TUDSSL/DIPS/int-debugger-firmware/src/gdb_main.c

/*
* This file is part of the Black Magic Debug project.
*
* Copyright (C) 2011  Black Sphere Technologies Ltd.
* Written by Gareth McMullin <gareth@blacksphere.co.nz>
*
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
* You should have received a copy of the GNU General Public License
* along with this program.  If not, see <http://www.gnu.org/licenses/>.
*/

/* This file implements the GDB Remote Serial Debugging protocol as
* described in "Debugging with GDB" build from GDB source.
*
* Originally written for GDB 6.8, updated and tested with GDB 7.2.
*/

#include "general.h"
#include "ctype.h"
#include "hex_utils.h"
#include "gdb_if.h"
#include "gdb_packet.h"
#include "gdb_main.h"
#include "gdb_hostio.h"
#include "target.h"
#include "command.h"
#include "crc32.h"
#include "morse.h"
#include "exception.h"
#include "spi.h"
#include <alloca.h>

enum gdb_signal {
   GDB_SIGINT = 2,
   GDB_SIGTRAP = 5,
   GDB_SIGSEGV = 11,
   GDB_SIGLOST = 29,
};

#define BUF_SIZE	1024U

#define ERROR_IF_NO_TARGET()	\
	if(!cur_target) { target_lost(); break; }

typedef struct
{
   const char *cmd_prefix;
   void (*func)(const char *packet, size_t len);
} cmd_executer;

static char pbuf[BUF_SIZE + 1U];

static target *cur_target;
static target *last_target;
static bool gdb_needs_detach_notify = false;

static void handle_q_packet(char *packet, size_t len);
static void handle_v_packet(char *packet, size_t len);
static void handle_z_packet(char *packet, size_t len);
static void handle_kill_target(void);

unsigned int times_intermittent = 0;
bool m_interrupt_on_power_failure = false;
arch_mode_t m_current_architecture = UNKNOWN_ARCH;
operation_mode_t m_debugger_mode = MODE_REGULAR;
bool disable_supply_after_next_continue = false;

static void gdb_target_destroy_callback(struct target_controller *tc, target *t)
{
   (void)tc;
   if (cur_target == t) {
       cur_target = NULL;
       gdb_needs_detach_notify = true;
   }

   if (last_target == t)
       last_target = NULL;
}

static void gdb_target_printf(struct target_controller *tc,
                             const char *fmt, va_list ap)
{
   (void)tc;
   gdb_voutf(fmt, ap);
}

static struct target_controller gdb_controller = {
   .destroy_callback = gdb_target_destroy_callback,
   .printf = gdb_target_printf,

   .open = hostio_open,
   .close = hostio_close,
   .read = hostio_read,
   .write = hostio_write,
   .lseek = hostio_lseek,
   .rename = hostio_rename,
   .unlink = hostio_unlink,
   .stat = hostio_stat,
   .fstat = hostio_fstat,
   .gettimeofday = hostio_gettimeofday,
   .isatty = hostio_isatty,
   .system = hostio_system,
};

void halt_gdb_main_loop(){
    target_addr_t watch;
    enum target_halt_reason reason;

    if (!cur_target) {
        /* Report "target exited" if no target */
        gdb_putpacketz("W00");
        return;
    }

    /* Wait for target halt */
    platform_timeout timeout;
Again:
    if(m_debugger_mode != MODE_PROFILE) disable_supply();
    while(!(reason = target_halt_poll(cur_target, &watch))) {
        if(false){
            char c = (char)gdb_if_getchar_to(0);
            if(c == '\x03' || c == '\x04')
            target_halt_request(cur_target);
        }
    }
    SET_RUN_STATE(0);

    /* Translate reason to GDB signal */
    switch (reason) {
        case TARGET_HALT_BREAKPOINT:
            if(m_debugger_mode != MODE_PROFILE) enable_supply();
            if(m_current_architecture != MSP_ARCH){
                // Not sure why this is implemented but it is unnessecary for the MSP arch
                platform_timeout_set(&timeout, 200);
                while ((reason = target_halt_poll(cur_target, &watch)) == TARGET_HALT_BREAKPOINT){
                    if (platform_timeout_is_expired(&timeout))
                        break;
                }
            }
            if (reason == TARGET_HALT_BREAKPOINT){
                gdb_putpacket_f("T%02X", GDB_SIGTRAP);
                break;
            } else if (reason != TARGET_HALT_INTERMITTENT){
                goto Again;
            }
            /* Fallthrough for TARGET_HALT_INTERMITTENT */
        case TARGET_HALT_INTERMITTENT:
            if(m_debugger_mode != MODE_PROFILE) disable_supply();
            if (intermittent_mode){
                morse("I.", false);
                target_lost();
            }
            else{
                gdb_putpacket_f("X%02X", GDB_SIGLOST);
                target_list_free_extended();
                morse("TARGET LOST.", true);
            }
            break;
        case TARGET_HALT_REQUEST:
            if(m_debugger_mode != MODE_PROFILE) enable_supply();
            gdb_putpacket_f("T%02X", GDB_SIGINT);
            break;
        case TARGET_HALT_WATCHPOINT:
            if(m_debugger_mode != MODE_PROFILE) enable_supply();
            gdb_putpacket_f("T%02Xwatch:%08X;", GDB_SIGTRAP, watch);
            break;
        case TARGET_HALT_FAULT:
            gdb_putpacket_f("T%02X", GDB_SIGSEGV);
            break;
        default:
            if(m_debugger_mode != MODE_PROFILE) enable_supply();
            gdb_putpacket_f("T%02X", GDB_SIGTRAP);
    }
}

int gdb_main_loop(struct target_controller *tc, bool in_syscall)
{
   bool single_step = false;

   /* GDB protocol main loop */
   while (1) {
       // When device was intermittent:
       if (!target_available()){
           // Reconnect procedure:
           // Check if device is reachable again or return
           // Reconnect:
           // Send SWD->JTAG command
           // Compare IDCODE with old IDCODE when different -> exception
           // Turn on Debug Port
           // Get AP en DP information from cache
           // Write AP select and unlock the AP's
           // Halt and Enable Supply
           // Reconfigure breakpoints
           // Continue execution + Disable Supply

           // Take note of the frees and memory allocations
           // Maybe when device is deattached, free more rather then when connection is lost
           target_list_free();

           SET_IDLE_STATE(false);
           SET_ERROR_STATE(true);
           int devs = -1;
           bool do_halt = false;
           volatile struct exception e;
           // Find the target or catch

           while(devs <= 0){
                char c = (char)gdb_if_getchar_to(0);
                if(c == '\x03' || c == '\x04'){
                    enable_supply();
                    do_halt = true;
                }
               
               TRY_CATCH (e, EXCEPTION_ALL) {
                switch (m_current_architecture)
                {
                    case MSP_ARCH:
                        devs = sbw_scan(0);                    
                        break;
                    case ARM_ARCH:
                        devs = adiv5_swdp_scan(0);
                        break;
                    default:
                        devs = adiv5_swdp_scan(0);
                        if(devs <= 0){
                                devs = sbw_scan(0);
                        }
                        break;
                }
               }
           }
           
           enable_supply();
           if(m_debugger_mode == MODE_PROFILE){
              disable_supply_after_next_continue = true;
           }

           SET_ERROR_STATE(false);
           times_intermittent++;

           // try reconnecting
           cur_target = target_attach_n(1, &gdb_controller);

           // retransmit breakpoints/watchpoints
           target_restore_breakpoints(cur_target);
           if (!do_halt && !m_interrupt_on_power_failure){
               target_halt_resume(cur_target, single_step);
               SET_RUN_STATE(true);
               halt_gdb_main_loop();
               break;
           }
           gdb_putpacket_f("T%02X", GDB_SIGINT);
       }

       SET_IDLE_STATE(1);
       size_t size = gdb_getpacket(pbuf, BUF_SIZE);
       // If port closed and target detached, stay idle
       if ((pbuf[0] != 0x04) || cur_target) {
           SET_IDLE_STATE(0);
       }
       switch(pbuf[0]) {
           /* Implementation of these is mandatory! */
           case 'g': { /* 'g': Read general registers */
               ERROR_IF_NO_TARGET();
               uint8_t gp_regs[target_regs_size(cur_target)];
               target_regs_read(cur_target, gp_regs);
               gdb_putpacket(hexify(pbuf, gp_regs, sizeof(gp_regs)), sizeof(gp_regs) * 2U);
               break;
           }
           case 'm': {	/* 'm addr,len': Read len bytes from addr */
               uint32_t addr, len;
               ERROR_IF_NO_TARGET();
               sscanf(pbuf, "m%" SCNx32 ",%" SCNx32, &addr, &len);
               if (len > sizeof(pbuf) / 2) {
                   gdb_putpacketz("E02");
                   break;
               }
               DEBUG_GDB("m packet: addr = %" PRIx32 ", len = %" PRIx32 "\n",
                         addr, len);
               uint8_t mem[len];
               if (target_mem_read(cur_target, mem, addr, len))
                   gdb_putpacketz("E01");
               else
                   gdb_putpacket(hexify(pbuf, mem, len), len * 2U);
               break;
           }
           case 'G': {	/* 'G XX': Write general registers */
               ERROR_IF_NO_TARGET();
               uint8_t gp_regs[target_regs_size(cur_target)];
               unhexify(gp_regs, &pbuf[1], sizeof(gp_regs));
               target_regs_write(cur_target, gp_regs);
               gdb_putpacketz("OK");
               break;
           }
           case 'M': { /* 'M addr,len:XX': Write len bytes to addr */
               uint32_t addr = 0;
               uint32_t len = 0;
               int hex;
               ERROR_IF_NO_TARGET();
               sscanf(pbuf, "M%" SCNx32 ",%" SCNx32 ":%n", &addr, &len, &hex);
               if (len > (unsigned)(size - hex) / 2) {
                   gdb_putpacketz("E02");
                   break;
               }
               DEBUG_GDB("M packet: addr = %" PRIx32 ", len = %" PRIx32 "\n",
                         addr, len);
               uint8_t mem[len];
               unhexify(mem, pbuf + hex, len);
               if (target_mem_write(cur_target, addr, mem, len))
                   gdb_putpacketz("E01");
               else
                   gdb_putpacketz("OK");
               break;
           }
           /* '[m|M|g|G|c][thread-id]' : Set the thread ID for the given subsequent operation
        * (we don't actually care which as we only care about the TID for whether to send OK or an error)
            */
           case 'H': {
               char operation = 0;
               uint32_t thread_id = 0;
               sscanf(pbuf, "H%c%" SCNx32, &operation, &thread_id);
               if (thread_id <= 1)
                   gdb_putpacketz("OK");
               else
                   gdb_putpacketz("E01");
               break;
           }
           case 's':	/* 's [addr]': Single step [start at addr] */
               single_step = true;
               /* fall through */
           case 'c':	/* 'c [addr]': Continue [at addr] */
               if (!cur_target) {
                   gdb_putpacketz("X1D");
                   break;
               }

               target_halt_resume(cur_target, single_step);
               SET_RUN_STATE(1);
               single_step = false;
               /* fall through */
           case '?': {	/* '?': Request reason for target halt */
               /* This packet isn't documented as being mandatory,
            * but GDB doesn't work without it. */
               halt_gdb_main_loop();
              break;
           }

           /* Optional GDB packet support */
           case 'p': { /* Read single register */
               ERROR_IF_NO_TARGET();
               uint32_t reg;
               sscanf(pbuf, "p%" SCNx32, &reg);
               uint8_t val[8];
               size_t s = target_reg_read(cur_target, reg, val, sizeof(val));
               if (s > 0)
                   gdb_putpacket(hexify(pbuf, val, s), s * 2);
               else
                   target_lost();
               break;
           }
           case 'P': { /* Write single register */
               ERROR_IF_NO_TARGET();
               uint32_t reg;
               int n;
               sscanf(pbuf, "P%" SCNx32 "=%n", &reg, &n);
               // TODO: FIXME, VLAs considered harmful.
               uint8_t val[strlen(&pbuf[n]) / 2];
               unhexify(val, pbuf + n, sizeof(val));
               if (target_reg_write(cur_target, reg, val, sizeof(val)) > 0)
                   gdb_putpacketz("OK");
               else
                   target_lost();
               break;
           }

           case 'F':	/* Semihosting call finished */
               if (in_syscall)
                   return hostio_reply(tc, pbuf, size);
               else {
                   DEBUG_GDB("*** F packet when not in syscall! '%s'\n", pbuf);
                   gdb_putpacketz("");
               }
               break;

           case '!':	/* Enable Extended GDB Protocol. */
               /* This doesn't do anything, we support the extended
            * protocol anyway, but GDB will never send us a 'R'
            * packet unless we answer 'OK' here.
                */
               gdb_putpacketz("OK");
               break;

           case 0x04:
           case 'D':	/* GDB 'detach' command. */
               if(cur_target) {
                   SET_RUN_STATE(1);
                   target_detach(cur_target);
                   last_target = cur_target;
                   target_list_free_extended();
                   cur_target = NULL;
               }
               if (pbuf[0] == 'D')
                   gdb_putpacketz("OK");

               if(m_debugger_mode != MODE_PROFILE) disable_supply();
               break;

           case 'k':	/* Kill the target */
               handle_kill_target();
               break;

           case 'r':	/* Reset the target system */
           case 'R':	/* Restart the target program */
               if (cur_target)
                   target_reset(cur_target);
               else if (last_target) {
                   cur_target = target_attach(last_target, &gdb_controller);
                   if (cur_target)
                       morse(NULL, false);
                   target_reset(cur_target);
               }
               break;

           case 'X': { /* 'X addr,len:XX': Write binary data to addr */
               uint32_t addr, len;
               int bin;
               ERROR_IF_NO_TARGET();
               sscanf(pbuf, "X%" SCNx32 ",%" SCNx32 ":%n", &addr, &len, &bin);
               if (len > (unsigned)(size - bin)) {
                   gdb_putpacketz("E02");
                   break;
               }
               DEBUG_GDB("X packet: addr = %" PRIx32 ", len = %" PRIx32 "\n",
                         addr, len);
               if (target_mem_write(cur_target, addr, pbuf + bin, len))
                   gdb_putpacketz("E01");
               else
                   gdb_putpacketz("OK");
               break;
           }

           case 'q':	/* General query packet */
               handle_q_packet(pbuf, size);
               break;

           case 'v':	/* Verbose command packet */
               handle_v_packet(pbuf, size);
               break;

           /* These packet implement hardware break-/watchpoints */
           case 'Z':	/* Z type,addr,len: Set breakpoint packet */
           case 'z':	/* z type,addr,len: Clear breakpoint packet */
               ERROR_IF_NO_TARGET();
               handle_z_packet(pbuf, size);
               break;

           default: 	/* Packet not implemented */
               DEBUG_GDB("*** Unsupported packet: %s\n", pbuf);
               gdb_putpacketz("");
       }
   }
}

static bool exec_command(char *packet, const size_t length, const cmd_executer *exec)
{
   while (exec->cmd_prefix) {
       const size_t prefix_length = strlen(exec->cmd_prefix);
       if (!strncmp(packet, exec->cmd_prefix, prefix_length)) {
           exec->func(packet + prefix_length, length - prefix_length);
           return true;
       }
       ++exec;
   }
   return false;
}

static void exec_q_rcmd(const char *packet, const size_t length)
{
   /* calculate size and allocate buffer for command */
   const size_t datalen = length / 2U;
   // This needs replacing with something more sensible.
   // It should be pinging -Wvla among other things, and it failing is straight-up UB
   char *data = alloca(datalen + 1);
   /* dehexify command */
   unhexify(data, packet, datalen);
   data[datalen] = 0;	/* add terminating null */

   const int c = command_process(cur_target, data);
   if (c < 0)
       gdb_putpacketz("");
   else if (c == 0)
       gdb_putpacketz("OK");
   else
       gdb_putpacket(hexify(pbuf, "Failed\n", strlen("Failed\n")),
                     2 * strlen("Failed\n"));
}

static void handle_q_string_reply(const char *reply, const char *param)
{
   const size_t reply_length = strlen(reply);
   uint32_t addr = 0;
   uint32_t len = 0;

   if (sscanf(param, "%08" PRIx32 ",%08" PRIx32, &addr, &len) != 2) {
       gdb_putpacketz("E01");
       return;
   }
   if (addr > reply_length) {
       gdb_putpacketz("E01");
       return;
   }
   if (addr == reply_length) {
       gdb_putpacketz("l");
       return;
   }
   size_t output_len = reply_length - addr;
   if (output_len > len)
       output_len = len;
   gdb_putpacket2("m", 1U, reply + addr, output_len);
}

static void exec_q_supported(const char *packet, const size_t length)
{
   (void)packet;
   (void)length;
   gdb_putpacket_f("PacketSize=%X;qXfer:memory-map:read+;qXfer:features:read+", BUF_SIZE);
}

static void exec_q_memory_map(const char *packet, const size_t length)
{
   (void)packet;
   (void)length;
   /* Read target XML memory map */
   if ((!cur_target) && last_target) {
       /* Attach to last target if detached. */
       cur_target = target_attach(last_target,
                                  &gdb_controller);
   }
   if (!cur_target) {
       gdb_putpacketz("E01");
       return;
   }
   char buf[1024];
   target_mem_map(cur_target, buf, sizeof(buf)); /* Fixme: Check size!*/
   handle_q_string_reply(buf, packet);
}

static void exec_q_feature_read(const char *packet, const size_t length)
{
   (void)length;
   /* Read target description */
   if ((!cur_target) && last_target) {
       /* Attach to last target if detached. */
       cur_target = target_attach(last_target, &gdb_controller);
   }
   if (!cur_target) {
       gdb_putpacketz("E01");
       return;
   }
   handle_q_string_reply(target_tdesc(cur_target), packet);
}

static void exec_q_crc(const char *packet, const size_t length)
{
   (void)length;
   uint32_t addr;
   uint32_t addr_length;
   if (sscanf(packet, "%" PRIx32 ",%" PRIx32, &addr, &addr_length) == 2) {
       if (!cur_target) {
           gdb_putpacketz("E01");
           return;
       }
       uint32_t crc;
       if (generic_crc32(cur_target, &crc, addr, addr_length))
           gdb_putpacketz("E03");
       else
           gdb_putpacket_f("C%lx", crc);
   }
}

/*
* qC queries are for the current thread. We don't support threads but GDB 11 and 12 require this,
* so we always answer that the current thread is thread 1.
*/
static void exec_q_c(const char *packet, const size_t length)
{
   (void)packet;
   (void)length;
   gdb_putpacketz("QC1");
}

/*
* qfThreadInfo queries are required in GDB 11 and 12 as these GDBs require the server to support
* threading even when there's only the possiblity for one thread to exist. In this instance,
* we have to tell GDB that there is a single active thread so it doesn't think the "thread" died.
* qsThreadInfo will always follow qfThreadInfo when we reply as we have to specify 'l' at the
* end to terminate the list.. GDB doesn't like this not happening.
*/
static void exec_q_thread_info(const char *packet, const size_t length)
{
   (void)length;
   if (packet[-11] == 'f')
       gdb_putpacketz("m1");
   else
       gdb_putpacketz("l");
}

static const cmd_executer q_commands[]=
   {
       {"qRcmd,",                         exec_q_rcmd},
       {"qSupported",                     exec_q_supported},
       {"qXfer:memory-map:read::",        exec_q_memory_map},
       {"qXfer:features:read:target.xml:",exec_q_feature_read},
       {"qCRC:",                          exec_q_crc},
       {"qC",                             exec_q_c},
       {"qfThreadInfo",                   exec_q_thread_info},
       {"qsThreadInfo",                   exec_q_thread_info},
       {NULL, NULL},
   };

static void handle_kill_target(void)
{
   if (cur_target) {
       target_reset(cur_target);
       target_detach(cur_target);
       last_target = cur_target;
       cur_target = NULL;
   }
}

static void handle_q_packet(char *packet, const size_t length)
{
   if (exec_command(packet, length, q_commands))
       return;
   DEBUG_GDB("*** Unsupported packet: %s\n", packet);
   gdb_putpacket("", 0);
}

static void handle_v_packet(char *packet, const size_t plen)
{
   uint32_t addr = 0;
   uint32_t len = 0;
   int bin;

   if (sscanf(packet, "vAttach;%08" PRIx32, &addr) == 1) {
       /* Attach to remote target processor */
       cur_target = target_attach_n(addr, &gdb_controller);
       if(cur_target) {
           morse(NULL, false);
           /*
            * We don't actually support threads, but GDB 11 and 12 can't work without
            * us saying we attached to thread 1.. see the following for the low-down of this:
            * https://sourceware.org/bugzilla/show_bug.cgi?id=28405
            * https://sourceware.org/bugzilla/show_bug.cgi?id=28874
            * https://sourceware.org/pipermail/gdb-patches/2021-December/184171.html
            * https://sourceware.org/pipermail/gdb-patches/2022-April/188058.html
            * https://sourceware.org/pipermail/gdb-patches/2022-July/190869.html
            */
           gdb_putpacketz("T05thread:1;");
       } else
           gdb_putpacketz("E01");

   } else if (!strncmp(packet, "vKill;", 6)) {
       /* Kill the target - we don't actually care about the PID that follows "vKill;" */
       handle_kill_target();
       gdb_putpacketz("OK");

   } else if (!strncmp(packet, "vRun", 4)) {
       /* Parse command line for get_cmdline semihosting call */
       char cmdline[83];
       char *pcmdline = cmdline;
       char *tok = packet + 4;
       if (*tok == ';')
           ++tok;
       cmdline[0] = '\0';
       while(*tok != '\0') {
           if (strlen(cmdline) + 3 >= sizeof(cmdline))
               break;
           if (*tok == ';') {
               *pcmdline++ = ' ';
               pcmdline[0] = '\0';
               tok++;
               continue;
           }
           if (isxdigit(tok[0]) && isxdigit(tok[1])) {
               unhexify(pcmdline, tok, 2);
               if ((*pcmdline == ' ') || (*pcmdline == '\\')) {
                   pcmdline[1] = *pcmdline;
                   *pcmdline++ = '\\';
               }
               pcmdline++;
               tok += 2;
               pcmdline[0] = '\0';
               continue;
           }
           break;
       }
       /* Run target program. For us (embedded) this means reset. */
       if (cur_target) {
           target_set_cmdline(cur_target, cmdline);
           target_reset(cur_target);
           gdb_putpacketz("T05");
       } else if (last_target) {
           cur_target = target_attach(last_target,
                                      &gdb_controller);

           /* If we were able to attach to the target again */
           if (cur_target) {
               target_set_cmdline(cur_target, cmdline);
               target_reset(cur_target);
               morse(NULL, false);
               gdb_putpacketz("T05");
           } else
               gdb_putpacketz("E01");

       } else
           gdb_putpacketz("E01");

   } else if (sscanf(packet, "vFlashErase:%08" PRIx32 ",%08" PRIx32, &addr, &len) == 2) {
       /* Erase Flash Memory */
       DEBUG_GDB("Flash Erase %08" PRIX32 " %08" PRIX32 "\n", addr, len);
       if (!cur_target) {
           gdb_putpacketz("EFF");
           return;
       }

       if (target_flash_erase(cur_target, addr, len))
           gdb_putpacketz("OK");
       else {
           target_flash_complete(cur_target);
           gdb_putpacketz("EFF");
       }

   } else if (sscanf(packet, "vFlashWrite:%08" PRIx32 ":%n", &addr, &bin) == 1) {
       /* Write Flash Memory */
       const uint32_t count = plen - bin;
       DEBUG_GDB("Flash Write %08" PRIX32 " %08" PRIX32 "\n", addr, count);
       if (cur_target && target_flash_write(cur_target, addr, (void*)packet + bin, count))
           gdb_putpacketz("OK");
       else {
           target_flash_complete(cur_target);
           gdb_putpacketz("EFF");
       }

   } else if (!strcmp(packet, "vFlashDone")) {
       /* Commit flash operations. */
       if (target_flash_complete(cur_target))
           gdb_putpacketz("OK");
       else
           gdb_putpacketz("EFF");

   } else if (!strcmp(packet, "vStopped")) {
       if (gdb_needs_detach_notify) {
           gdb_putpacketz("W00");
           gdb_needs_detach_notify = false;
       } else
           gdb_putpacketz("OK");

   } else {
       /* The vMustReplyEmpty is used as a feature test to check how gdbserver handles unknown packets */
       /* print only actually unknown packets */
       if (strcmp(packet, "vMustReplyEmpty") != 0)
           DEBUG_GDB("*** Unsupported packet: %s\n", packet);
       gdb_putpacket("", 0);
   }
}

static void handle_z_packet(char *packet, const size_t plen)
{
   (void)plen;

   uint32_t type;
   uint32_t len;
   uint32_t addr;
   sscanf(packet, "%*[zZ]%" PRIu32 ",%08" PRIx32 ",%" PRIu32, &type, &addr, &len);

   int ret = 0;
   if (packet[0] == 'Z')
       ret = target_breakwatch_set(cur_target, type, addr, len, true);
   else
       ret = target_breakwatch_clear(cur_target, type, addr, len);

   if (ret < 0)
       gdb_putpacketz("E01");
   else if (ret > 0)
       gdb_putpacketz("");
   else
       gdb_putpacketz("OK");
}

void gdb_main(void)
{
   gdb_main_loop(&gdb_controller, false);
}
