TUDSSL/DIPS/int-debugger-firmware/include/platforms/native/platform.h

/*
 * This file is part of the Black Magic Debug project.
 *
 * Copyright (C) 2011  Black Sphere Technologies Ltd.
 * Written by Gareth McMullin <gareth@blacksphere.co.nz>
 *
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
 * You should have received a copy of the GNU General Public License
 * along with this program.  If not, see <http://www.gnu.org/licenses/>.
 */

/* This file implements the platform specific functions for the STM32
 * implementation.
 */
#ifndef __PLATFORM_H
#define __PLATFORM_H

#include "platforms/stm32/gpio.h"
#include "timing.h"
#include "platforms/stm32/timing_stm32.h"

#define PLATFORM_HAS_TRACESWO
#define PLATFORM_HAS_POWER_SWITCH
#define PLATFORM_HAS_USBUART

#ifdef ENABLE_DEBUG
# define PLATFORM_HAS_DEBUG
# define USBUART_DEBUG
extern bool debug_bmp;
int usbuart_debug_write(const char *buf, size_t len);
#endif

#define PLATFORM_IDENT          " "
#define UPD_IFACE_STRING        "@Internal Flash   /0x08000000/8*001Kg"

/* Important pin mappings for STM32 implementation:
 *
 * LED0 = 	PB2	(Yellow LED : Running)
 * LED1 = 	PB10	(Yellow LED : Idle)
 * LED2 = 	PB11	(Red LED    : Error)
 *
 * TPWR = 	PB0 (input) -- analogue on mini design ADC1, ch8
 * nTRST = 	PB1 (output) [blackmagic]
 * PWR_BR = 	PB1 (output) [blackmagic_mini] -- supply power to the target, active low
 * TMS_DIR =    PA1 (output) [blackmagic_mini v2.1] -- choose direction of the TCK pin, input low, output high
 * SRST_OUT = 	PA2 (output)
 * TDI = 	PA3 (output)
 * TMS = 	PA4 (input/output for SWDIO)
 * TCK = 	PA5 (output SWCLK)
 * TDO = 	PA6 (input)
 * nSRST = 	PA7 (input)
 *
 * USB cable pull-up: PA8
 * USB VBUS detect:  PB13 -- New on mini design.
 *                           Enable pull up for compatibility.
 * Force DFU mode button: PB12
 */

#define HW_SWITCH(ver, opt1, opt2) \
	((platform_hwversion() < (ver))?(opt1):(opt2))

/* Hardware definitions... */
#define JTAG_PORT 	GPIOA
#define TDI_PORT	JTAG_PORT
#define TMS_DIR_PORT	JTAG_PORT
#define TMS_PORT	JTAG_PORT
#define TCK_PORT	JTAG_PORT
#define TDO_PORT	JTAG_PORT
#define TDI_PIN		GPIO3
#define TMS_DIR_PIN	GPIO1
#define TMS_PIN		GPIO4
#define TCK_PIN		GPIO5
#define TDO_PIN		GPIO6

#define SWDIO_DIR_PORT	JTAG_PORT
#define SWDIO_PORT 	JTAG_PORT
#define SWCLK_PORT 	JTAG_PORT
#define SWDIO_DIR_PIN	TMS_DIR_PIN
#define SWDIO_PIN	TMS_PIN
#define SWCLK_PIN	TCK_PIN

#define TRST_PORT	GPIOB
#define TRST_PIN	GPIO1
#define PWR_BR_PORT	GPIOB
#define PWR_BR_PIN	GPIO1

#define NRST_PORT	GPIOA
#define NRST_PIN	HW_SWITCH(6, GPIO2, GPIO9)
#define NRST_SENSE_PORT	GPIOA
#define NRST_SENSE_PIN  HW_SWITCH(6, GPIO7, GPIO13)

#define SRST_PORT	GPIOA
#define SRST_PIN	GPIO2
#define SRST_SENSE_PORT	GPIOA
#define SRST_SENSE_PIN	GPIO7

#define USB_PU_PORT	GPIOA
#define USB_PU_PIN	GPIO8

/* For HW Rev 4 and older */
#define USB_VBUS_PORT	GPIOB
#define USB_VBUS_PIN	GPIO13
/* IRQ stays the same for all hw revisions. */
#define USB_VBUS_IRQ	NVIC_EXTI15_10_IRQ

/* For HW Rev 5 and newer */
#define USB_VBUS5_PORT	GPIOA
#define USB_VBUS5_PIN	GPIO15

#define LED_PORT	GPIOB
#define LED_PORT_UART	GPIOB
#define LED_0		GPIO2
#define LED_1		GPIO10
#define LED_2		GPIO8
#define LED_UART	LED_0
#define LED_IDLE_RUN	LED_1
#define LED_ERROR	LED_2

#define BUS_IO_EN_PORT GPIOC
#define BUS_IO_EN_PIN GPIO8
#define BUS_INT_EN_PORT GPIOC
#define BUS_INT_EN_PIN GPIO9

#define SPI SPI2
#define SPI_RCC RCC_SPI2
#define SPI_PORT GPIOB
#define SPI_SS_PIN GPIO12
#define SPI_SCK_PIN GPIO13
#define SPI_MISO_PIN GPIO14
#define SPI_MOSI_PIN GPIO15

#define P_INT_PORT GPIOC
#define P_INT_PIN GPIO6
#define P_INT_2_PIN GPIO7

#define DEBUGGER_PINS_PORT GPIOC
#define DEBUGGER_TX_PIN GPIO5
#define DEBUGGER_RX_PIN GPIO4

# define SWD_CR   GPIO_CRL(SWDIO_PORT)
# define SWD_CR_MULT (1 << (4 << 2))

#define TMS_SET_MODE() do { \
	gpio_set(TMS_DIR_PORT, TMS_DIR_PIN); \
	gpio_set_mode(TMS_PORT, GPIO_MODE_OUTPUT_50_MHZ, \
	              GPIO_CNF_OUTPUT_PUSHPULL, TMS_PIN); \
} while(0)

#define TMS_SET_MODE_OUTPUT() do { \
  gpio_set(TMS_DIR_PORT, TMS_DIR_PIN); \
  gpio_set_mode(TMS_PORT, GPIO_MODE_OUTPUT_50_MHZ, \
                GPIO_CNF_OUTPUT_PUSHPULL, TMS_PIN); \
} while(0)

#define TMS_SET_MODE_INPUT() do { \
  gpio_clear(TMS_DIR_PORT, TMS_DIR_PIN); \
  gpio_set_mode(TMS_PORT, GPIO_MODE_INPUT, \
                GPIO_CNF_INPUT_FLOAT, TMS_PIN); \
} while(0)


#define SWDIO_MODE_FLOAT() do { \
	uint32_t cr = SWD_CR; \
	cr  &= ~(0xf * SWD_CR_MULT); \
	cr  |=  (0x4 * SWD_CR_MULT); \
	GPIO_BRR(SWDIO_DIR_PORT) = SWDIO_DIR_PIN; \
	SWD_CR = cr; \
} while(0)
#define SWDIO_MODE_DRIVE() do { \
	uint32_t cr = SWD_CR; \
	cr  &= ~(0xf * SWD_CR_MULT); \
	cr  |=  (0x1 * SWD_CR_MULT); \
	GPIO_BSRR(SWDIO_DIR_PORT) = SWDIO_DIR_PIN; \
	SWD_CR = cr; \
} while(0)
#define UART_PIN_SETUP() do { \
	gpio_set_mode(USBUSART_PORT, GPIO_MODE_OUTPUT_2_MHZ, \
	              GPIO_CNF_OUTPUT_ALTFN_PUSHPULL, USBUSART_TX_PIN); \
} while(0)

#define USB_DRIVER st_usbfs_v1_usb_driver
#define USB_IRQ    NVIC_USB_LP_CAN_RX0_IRQ
#define USB_ISR    usb_lp_can_rx0_isr
/* Interrupt priorities.  Low numbers are high priority.
 * For now USART1 preempts USB which may spin while buffer is drained.
 * TIM3 is used for traceswo capture and must be highest priority.
 */

#define IRQ_PRI_USB             (1 << 4)
#define IRQ_PRI_USBUSART        (2 << 4)
#define IRQ_PRI_USBUSART_DMA 	(2 << 4)
#define IRQ_PRI_USB_VBUS        (14 << 4)
#define IRQ_PRI_TRACE           (0 << 4)

#define USBUSART HW_SWITCH(6, USBUSART1, USBUSART2)
#define USBUSART_IRQ HW_SWITCH(6, NVIC_USART1_IRQ, NVIC_USART2_IRQ)
#define USBUSART_CLK HW_SWITCH(6, RCC_USART1, RCC_USART2)
#define USBUSART_PORT GPIOA
#define USBUSART_TX_PIN HW_SWITCH(6, GPIO9, GPIO2)
#define USBUSART_RX_PIN HW_SWITCH(6, GPIO10, GPIO3)

#define USBUSART_DMA_BUS DMA1
#define USBUSART_DMA_CLK RCC_DMA1
#define USBUSART_DMA_TX_CHAN HW_SWITCH(6, USBUSART1_DMA_TX_CHAN, USBUSART2_DMA_TX_CHAN)
#define USBUSART_DMA_RX_CHAN HW_SWITCH(6, USBUSART1_DMA_RX_CHAN, USBUSART2_DMA_RX_CHAN)
#define USBUSART_DMA_TX_IRQ HW_SWITCH(6, USBUSART1_DMA_TX_IRQ, USBUSART2_DMA_TX_IRQ)
#define USBUSART_DMA_RX_IRQ HW_SWITCH(6, USBUSART1_DMA_RX_IRQ, USBUSART2_DMA_RX_IRQ)

#define USBUSART1 USART1
#define USBUSART1_IRQ NVIC_USART1_IRQ
#define USBUSART1_ISR(x) usart1_isr(x)
#define USBUSART1_DMA_TX_CHAN DMA_CHANNEL4
#define USBUSART1_DMA_TX_IRQ NVIC_DMA1_CHANNEL4_IRQ
#define USBUSART1_DMA_TX_ISR(x) dma1_channel4_isr(x)
#define USBUSART1_DMA_RX_CHAN DMA_CHANNEL5
#define USBUSART1_DMA_RX_IRQ NVIC_DMA1_CHANNEL5_IRQ
#define USBUSART1_DMA_RX_ISR(x) dma1_channel5_isr(x)

#define USBUSART2 USART2
#define USBUSART2_IRQ NVIC_USART2_IRQ
#define USBUSART2_ISR(x) usart2_isr(x)
#define USBUSART2_DMA_TX_CHAN DMA_CHANNEL7
#define USBUSART2_DMA_TX_IRQ NVIC_DMA1_CHANNEL7_IRQ
#define USBUSART2_DMA_TX_ISR(x) dma1_channel7_isr(x)
#define USBUSART2_DMA_RX_CHAN DMA_CHANNEL6
#define USBUSART2_DMA_RX_IRQ NVIC_DMA1_CHANNEL6_IRQ
#define USBUSART2_DMA_RX_ISR(x) dma1_channel6_isr(x)

#define TRACE_TIM TIM3
#define TRACE_TIM_CLK_EN() rcc_periph_clock_enable(RCC_TIM3)
#define TRACE_IRQ   NVIC_TIM3_IRQ
#define TRACE_ISR(x)  tim3_isr(x)

#define SET_RUN_STATE(state)	{running_status = (state);}
#define SET_IDLE_STATE(state)	{gpio_set_val(LED_PORT, LED_IDLE_RUN, state);}
#define SET_ERROR_STATE(state)	{gpio_set_val(LED_PORT, LED_ERROR, state);}

/*
 * Use newlib provided integer only stdio functions
 */

/* sscanf */
#ifdef sscanf
#undef sscanf
#define sscanf siscanf
#else
#define sscanf siscanf
#endif
/* sprintf */
#ifdef sprintf
#undef sprintf
#define sprintf siprintf
#else
#define sprintf siprintf
#endif
/* vasprintf */
#ifdef vasprintf
#undef vasprintf
#define vasprintf vasiprintf
#else
#define vasprintf vasiprintf
#endif
/* snprintf */
#ifdef snprintf
#undef snprintf
#define snprintf sniprintf
#else
#define snprintf sniprintf
#endif

uint16_t platform_dut_mv(void);
void setup_dips_irq(void);

#endif
