TUDSSL/DIPS/int-debugger-firmware/src/platforms/native/platform.c

#include "general.h"
#include "platforms/common/usbuart.h"
#include "morse.h"
#include "platforms/common/usb.h"
#include "spi.h"
#include "platforms/common/aux_serial.h"
#include "gdb_main.h"
#include "utils/stopwatch.h"

#include <libopencm3/stm32/rcc.h>
#include <libopencm3/cm3/scb.h>
#include <libopencm3/cm3/scs.h>
#include <libopencm3/cm3/nvic.h>
#include <libopencm3/stm32/exti.h>
#include <libopencm3/stm32/usart.h>
#include <libopencm3/usb/usbd.h>
#include <libopencm3/stm32/adc.h>

static void adc_init(void);
static void setup_vbus_irq(void);

#define BMP_HWVERSION_BYTE FLASH_OPTION_BYTE_2

/* Pins PB[7:5] are used to detect hardware revision.
 * 000 - Original production build.
 * 001 - Mini production build.
 * 010 - Mini V2.0e and later.
 * 011 - Mini V2.1e and later.
 */
int platform_hwversion(void)
{
    static int hwversion = -1;
    uint16_t hwversion_pins = GPIO7 | GPIO6 | GPIO5;
    uint16_t unused_pins = hwversion_pins ^ 0xFFFF;

    /* Only check for version if this is the first time. */
    if (hwversion == -1) {
        /* Configure the hardware version pins as input pull-up/down */
        gpio_set_mode(GPIOB, GPIO_MODE_INPUT,
                      GPIO_CNF_INPUT_PULL_UPDOWN,
                      hwversion_pins);

        /* Enable the weak pull up. */
        gpio_set(GPIOB, hwversion_pins);

        /* Wait a little to make sure the pull up is in effect... */
        for(int i = 0; i < 100; i++) asm("nop");

        /* Get all pins that are pulled low in hardware.
         * This also sets all the "unused" pins to 1.
         */
        uint16_t pins_negative = gpio_get(GPIOB, hwversion_pins) | unused_pins;

        /* Enable the weak pull down. */
        gpio_clear(GPIOB, hwversion_pins);

        /* Wait a little to make sure the pull down is in effect... */
        for(int i = 0; i < 100; i++) asm("nop");

        /* Get all the pins that are pulled high in hardware. */
        uint16_t pins_positive = gpio_get(GPIOB, hwversion_pins);

        /* Hardware version is the id defined by the pins that are
         * asserted low or high by the hardware. This means that pins
         * that are left floating are 0 and those that are either
         * pulled high or low are 1.
         */
        hwversion = (((pins_positive ^ pins_negative) ^ 0xFFFF) & hwversion_pins) >> 5;
    }

    return hwversion;
}

void platform_init(void){
    SCS_DEMCR |= SCS_DEMCR_VC_MON_EN;
    rcc_clock_setup_in_hse_8mhz_out_72mhz();

    rcc_periph_clock_enable(RCC_USB);
    rcc_periph_clock_enable(RCC_GPIOA);
    rcc_periph_clock_enable(RCC_GPIOB);
    rcc_periph_clock_enable(RCC_AFIO);
    rcc_periph_clock_enable(RCC_CRC);

    /* Setup GPIO ports */
    gpio_clear(USB_PU_PORT, USB_PU_PIN);
    gpio_set_mode(USB_PU_PORT, GPIO_MODE_INPUT, GPIO_CNF_INPUT_FLOAT, USB_PU_PIN);

    gpio_set_mode(JTAG_PORT, GPIO_MODE_OUTPUT_50_MHZ, GPIO_CNF_OUTPUT_PUSHPULL, TMS_DIR_PIN | TCK_PIN | TDI_PIN);
    gpio_set_mode(JTAG_PORT, GPIO_MODE_OUTPUT_50_MHZ, GPIO_CNF_INPUT_FLOAT, TMS_PIN);
    /* This needs some fixing... */
    /* Toggle required to sort out line drivers... */
    gpio_port_write(GPIOA, 0x8102);
    gpio_port_write(GPIOB, 0x2000);

    gpio_port_write(GPIOA, 0x8182);
    gpio_port_write(GPIOB, 0x2002);

    gpio_set_mode(LED_PORT, GPIO_MODE_OUTPUT_2_MHZ, GPIO_CNF_OUTPUT_PUSHPULL, LED_UART | LED_IDLE_RUN | LED_ERROR);

    rcc_periph_clock_enable(RCC_GPIOC);
    gpio_set_mode(BUS_IO_EN_PORT, GPIO_MODE_OUTPUT_2_MHZ,
                  GPIO_CNF_OUTPUT_PUSHPULL,
                  BUS_IO_EN_PIN | BUS_INT_EN_PIN);

    gpio_set(BUS_IO_EN_PORT, BUS_IO_EN_PIN);
    gpio_set(BUS_IO_EN_PORT, BUS_INT_EN_PIN);

    /* Configure P_INT as output for supply */
    gpio_set_mode(P_INT_PORT, GPIO_MODE_OUTPUT_10_MHZ,
                  GPIO_CNF_OUTPUT_PUSHPULL, P_INT_PIN);
    gpio_set_mode(P_INT_PORT, GPIO_MODE_INPUT,
                  GPIO_CNF_INPUT_FLOAT, P_INT_2_PIN);

    /* Configure RX and TX to the DUT */
    gpio_set_mode(DEBUGGER_PINS_PORT, GPIO_MODE_OUTPUT_10_MHZ,
                  GPIO_CNF_OUTPUT_PUSHPULL, DEBUGGER_TX_PIN); 

    gpio_set_mode(DEBUGGER_PINS_PORT, GPIO_MODE_INPUT,
                  GPIO_CNF_INPUT_PULL_UPDOWN, DEBUGGER_RX_PIN);  
    setup_dips_irq();

    /* Enable SRST output. Original uses a NPN to pull down, so setting the
     * output HIGH asserts. Mini is directly connected so use open drain output
     * and set LOW to assert.
     */
    platform_nrst_set_val(false);
    gpio_set_mode(NRST_PORT, GPIO_MODE_OUTPUT_50_MHZ,
                  (((platform_hwversion() == 0) || (platform_hwversion() >= 3)) ? GPIO_CNF_OUTPUT_PUSHPULL
                                                                                  : GPIO_CNF_OUTPUT_OPENDRAIN),
                  NRST_PIN);
    /* FIXME: Gareth, Esden, what versions need this fix? */
    if (platform_hwversion() < 3)
        /* FIXME: This pin in intended to be input, but the TXS0108 fails
		 * to release the device from reset if this floats. */
        gpio_set_mode(NRST_SENSE_PORT, GPIO_MODE_OUTPUT_2_MHZ, GPIO_CNF_OUTPUT_PUSHPULL, NRST_SENSE_PIN);
    else {
        gpio_set(NRST_SENSE_PORT, NRST_SENSE_PIN);
        gpio_set_mode(NRST_SENSE_PORT, GPIO_MODE_INPUT, GPIO_CNF_INPUT_PULL_UPDOWN, NRST_SENSE_PIN);
    }
    /* Enable internal pull-up on PWR_BR so that we don't drive
       TPWR locally or inadvertently supply power to the target. */
    if (platform_hwversion() == 1) {
        gpio_set(PWR_BR_PORT, PWR_BR_PIN);
        gpio_set_mode(PWR_BR_PORT, GPIO_MODE_INPUT, GPIO_CNF_INPUT_PULL_UPDOWN, PWR_BR_PIN);
    } else if (platform_hwversion() > 1) {
        gpio_set(PWR_BR_PORT, PWR_BR_PIN);
        gpio_set_mode(PWR_BR_PORT, GPIO_MODE_OUTPUT_50_MHZ, GPIO_CNF_OUTPUT_OPENDRAIN, PWR_BR_PIN);
    }

    if (platform_hwversion() > 0) {
        adc_init();
    } else {
        gpio_clear(GPIOB, GPIO0);
        gpio_set_mode(GPIOB, GPIO_MODE_INPUT,
                      GPIO_CNF_INPUT_PULL_UPDOWN, GPIO0);
    }
    /* Relocate interrupt vector table here */
    extern int vector_table;
    SCB_VTOR = (uint32_t)&vector_table;

    platform_timing_init();
    blackmagic_usb_init();

    // We use ss pin for interrupt
//    gpio_set_mode(SPI_PORT, GPIO_MODE_OUTPUT_50_MHZ, GPIO_CNF_OUTPUT_ALTFN_PUSHPULL,
//                  SPI_SS_PIN);
    gpio_clear(SPI_PORT, SPI_SS_PIN);

    if (platform_hwversion() == 0 || platform_hwversion() >= 3 || !(SCS_DEMCR & SCS_DEMCR_TRCENA))
        aux_serial_init();

    setup_vbus_irq();
    spi_init();

}

void platform_nrst_set_val(bool assert)
{
    gpio_set(TMS_PORT, TMS_PIN);
    if ((platform_hwversion() == 0) ||
       (platform_hwversion() >= 3)) {
        gpio_set_val(NRST_PORT, NRST_PIN, assert);
    } else {
        gpio_set_val(NRST_PORT, NRST_PIN, !assert);
    }
    if (assert) {
        for(int i = 0; i < 10000; i++) __asm__("nop");
    }
}

void platform_target_clk_output_enable(bool enable) {}

bool platform_nrst_get_val(void)
{
    if (platform_hwversion() == 0) {
        return gpio_get(NRST_SENSE_PORT, NRST_SENSE_PIN) == 0;
    } else if (platform_hwversion() >= 3) {
        return gpio_get(NRST_SENSE_PORT, NRST_SENSE_PIN) != 0;
    } else {
        return gpio_get(NRST_PORT, NRST_PIN) == 0;
    }
}

bool platform_target_get_power(void)
{
    if (platform_hwversion() > 0) {
        return !gpio_get(PWR_BR_PORT, PWR_BR_PIN);
    }
    return 0;
}

void platform_target_set_power(const bool power)
{
    if (platform_hwversion() > 0) {
        gpio_set_val(PWR_BR_PORT, PWR_BR_PIN, !power);
    }
}

static void adc_init(void)
{
    rcc_periph_clock_enable(RCC_ADC1);

    gpio_set_mode(GPIOB, GPIO_MODE_INPUT, GPIO_CNF_INPUT_ANALOG, GPIO0);

    adc_power_off(ADC1);
    adc_disable_scan_mode(ADC1);
    adc_set_continuous_conversion_mode(ADC1);
    adc_disable_external_trigger_regular(ADC1);
    adc_set_right_aligned(ADC1);
    adc_set_sample_time_on_all_channels(ADC1, ADC_SMPR_SMP_239DOT5CYC);

    adc_power_on(ADC1);

    /* Wait for ADC starting up. */
    for (int i = 0; i < 800000; i++)    /* Wait a bit. */
        __asm__("nop");

    adc_reset_calibration(ADC1);
    adc_calibrate(ADC1);

    const uint8_t channel = 8;
    adc_set_regular_sequence(ADC1, 1, (uint8_t*)&channel);
}


const char *platform_target_voltage(void)
{
    if (platform_hwversion() == 0)
        return gpio_get(GPIOB, GPIO0) ? "OK" : "ABSENT!";

    static char ret[] = "0.0V";
    const uint8_t channel = 8;
    adc_set_regular_sequence(ADC1, 1, (uint8_t*)&channel);

    adc_start_conversion_direct(ADC1);

    /* Wait for end of conversion. */
    while (!adc_eoc(ADC1));

    uint32_t val = adc_read_regular(ADC1) * 99; /* 0-4095 */
    ret[0] = '0' + val / 81910;
    ret[2] = '0' + (val / 8191) % 10;

    return ret;
}

uint16_t platform_dut_mv(void)
{
    uint32_t val = adc_read_regular(ADC1) * 99; /* 0-4095 */
    return (uint16_t) ((float)val / 81.910);
}

void platform_request_boot(void)
{
    /* Disconnect USB cable */
    gpio_set_mode(USB_PU_PORT, GPIO_MODE_INPUT, 0, USB_PU_PIN);

    /* Drive boot request pin */
    gpio_set_mode(GPIOB, GPIO_MODE_OUTPUT_2_MHZ,
                  GPIO_CNF_OUTPUT_PUSHPULL, GPIO9);
    gpio_clear(GPIOB, GPIO9);
}


uint32_t platform_target_voltage_sense(void)
{
    /* returns the voltage in volt scaled by 10 (so 33 means 3.3V), except
	 * for hardware version 1
	 * this function is only needed for implementations that allow the
	 * target to be powered from the debug probe
     */
    if (platform_hwversion() == 0)
        return 0;

    const uint8_t channel = 8;
    adc_set_regular_sequence(ADC1, 1, (uint8_t*)&channel);

    adc_start_conversion_direct(ADC1);

    /* Wait for end of conversion. */
    while (!adc_eoc(ADC1));

    uint32_t val = adc_read_regular(ADC1); /* 0-4095 */
    /* Clear EOC bit. The GD32F103 does not automatically reset it on ADC read. */
    ADC_SR(ADC1) &= ~ADC_SR_EOC;
    return (val * 99) / 8191;
}

void exti15_10_isr(void)
{
    uint32_t usb_vbus_port;
    uint16_t usb_vbus_pin;

    if (platform_hwversion() < 5) {
        usb_vbus_port = USB_VBUS_PORT;
        usb_vbus_pin = USB_VBUS_PIN;
    } else {
        usb_vbus_port = USB_VBUS5_PORT;
        usb_vbus_pin = USB_VBUS5_PIN;
    }

    if (gpio_get(usb_vbus_port, usb_vbus_pin)) {
        /* Drive pull-up high if VBUS connected */
        gpio_set_mode(USB_PU_PORT, GPIO_MODE_OUTPUT_10_MHZ,
                      GPIO_CNF_OUTPUT_PUSHPULL, USB_PU_PIN);
    } else {
        /* Allow pull-up to float if VBUS disconnected */
        gpio_set_mode(USB_PU_PORT, GPIO_MODE_INPUT,
                      GPIO_CNF_INPUT_FLOAT, USB_PU_PIN);
    }

    exti_reset_request(usb_vbus_pin);
}

static void setup_vbus_irq(void)
{
    uint32_t usb_vbus_port;
    uint16_t usb_vbus_pin;

    if (platform_hwversion() < 5) {
        usb_vbus_port = USB_VBUS_PORT;
        usb_vbus_pin = USB_VBUS_PIN;
    } else {
        usb_vbus_port = USB_VBUS5_PORT;
        usb_vbus_pin = USB_VBUS5_PIN;
    }

    nvic_set_priority(USB_VBUS_IRQ, IRQ_PRI_USB_VBUS);
    nvic_enable_irq(USB_VBUS_IRQ);

    gpio_set(usb_vbus_port, usb_vbus_pin);
    gpio_set(USB_PU_PORT, USB_PU_PIN);

    gpio_set_mode(usb_vbus_port, GPIO_MODE_INPUT,
                  GPIO_CNF_INPUT_PULL_UPDOWN, usb_vbus_pin);

    /* Configure EXTI for USB VBUS monitor */
    exti_select_source(usb_vbus_pin, usb_vbus_port);
    exti_set_trigger(usb_vbus_pin, EXTI_TRIGGER_BOTH);
    exti_enable_request(usb_vbus_pin);

    exti15_10_isr();
}


void profile_mode_pin_iqr_handler(uint16_t tx_value, uint16_t rx_value){
     if(!tx_value){
        // Device is not under JTAG control, ignore debugger updates 
        exti_reset_request(EXTI4);
        return;
    }

    // Check if ISR was triggered by fallingedge
    rx_value = gpio_get(DEBUGGER_PINS_PORT, DEBUGGER_RX_PIN);
    if (rx_value  != 0) {
        resume_stopwatch();
        enable_supply();
    } else  {
        halt_stopwatch();
        disable_supply();
    }
    
}

void passive_mode_pin_iqr_handler(uint16_t tx_value, uint16_t rx_value){
    if (rx_value  != 0 || tx_value != 0) {
        setEnergyGuard(false);
        enable_supply();
    } else  {
        clearEnergyGuard();
        disable_supply();
    }
}

void exti4_isr(void)
{
    // Only passive and profile mode need to interact with the dut pins directly
    if(m_debugger_mode != MODE_PROFILE && m_debugger_mode != MODE_PASSIVE){
        exti_reset_request(EXTI4);
        return;
    }

    uint16_t tx_value = gpio_get(DEBUGGER_PINS_PORT, DEBUGGER_TX_PIN);
    uint16_t rx_value = gpio_get(DEBUGGER_PINS_PORT, DEBUGGER_RX_PIN);

    switch (m_debugger_mode) {
        case MODE_PASSIVE:
            passive_mode_pin_iqr_handler(tx_value, rx_value);
            break;
        case MODE_PROFILE:
            profile_mode_pin_iqr_handler(tx_value, rx_value);
            break;
        default:
            break;
    }
   
    // Clear the EXTI interrupt flag
    exti_reset_request(EXTI4);
}

void setup_dips_irq(void)
{
    nvic_enable_irq(NVIC_EXTI4_IRQ);
    nvic_set_priority(NVIC_EXTI4_IRQ, 1);

    exti_select_source(EXTI4, DEBUGGER_PINS_PORT);
    exti_set_trigger(EXTI4, EXTI_TRIGGER_BOTH);
    exti_enable_request(EXTI4);

    // enable timer for stopwatch
    init_stopwatch();
}
