TUDSSL/DIPS/int-debugger-console/swolisten.c

/*
 * SWO Splitter for Blackmagic Probe and others.
 * =============================================
 *
 * This file is part of the Black Magic Debug project.
 *
 * Copyright (C) 2017  Dave Marples  <dave@marples.net>
 *
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
 * You should have received a copy of the GNU General Public License
 * along with this program.  If not, see <http://www.gnu.org/licenses/>.
 */


#include <stdlib.h>
#include <unistd.h>
#include <fcntl.h>
#include <ctype.h>
#include <sys/socket.h>
#include <sys/types.h>
#include <sys/ioctl.h>
#include <sys/stat.h>
#include <sys/wait.h>
#include <stdio.h>
#include <string.h>
#include <libusb-1.0/libusb.h>
#include <stdint.h>
#include <limits.h>
#include <termios.h>
#include <signal.h>

#define VID       (0x1d50)
#define PID       (0x6018)
#define INTERFACE (5)
#define ENDPOINT  (0x85)

#define TRANSFER_SIZE (64)
#define NUM_FIFOS     32
#define MAX_FIFOS     128

#define CHANNELNAME   "chan"

#define BOOL       char
#define FALSE      (0)
#define TRUE       (!FALSE)

// Record for options, either defaults or from command line
struct
{
  BOOL verbose;
  BOOL dump;
  int nChannels;
  char *chanPath;
  char *port;
  int speed;
} options = {.nChannels=NUM_FIFOS, .chanPath="", .speed=115200};

// Runtime state
struct
{
  int fifo[MAX_FIFOS];
} _r;

// ====================================================================================================
// ====================================================================================================
// ====================================================================================================
// Internals
// ====================================================================================================
// ====================================================================================================
// ====================================================================================================
static BOOL _runFifo(int portNo, int listenHandle, char *fifoName)

{
  int pid,fifo;
  int readDataLen, writeDataLen;

  if (mkfifo(fifoName,0666)<0)
    {
      return FALSE;
    }

  pid=fork();

  if (pid==0)
    {
      char rxdata[TRANSFER_SIZE];
      int fifo;

      /* Don't kill this sub-process when any reader or writer evaporates */
      signal(SIGPIPE, SIG_IGN);

      while (1)
	{
	  /* This is the child */
	  fifo=open(fifoName,O_WRONLY);

	  while (1)
	    {
	      readDataLen=read(listenHandle,rxdata,TRANSFER_SIZE);
	      if (readDataLen<=0)
		{
		  exit(0);
		}

	      writeDataLen=write(fifo,rxdata,readDataLen);
	      if (writeDataLen<=0)
		{
		  break;
		}
	    }
	  close(fifo);
	}
    }
  else if (pid<0)
    {
      /* The fork failed */
      return FALSE;
    }
  return TRUE;
}
// ====================================================================================================
static BOOL _makeFifoTasks(void)

/* Create each sub-process that will handle a port */

{
  char fifoName[PATH_MAX];

  int f[2];

  for (int t=0; t<options.nChannels; t++)
    {
      if (pipe(f)<0)
	  return FALSE;
      fcntl(f[1],F_SETFL,O_NONBLOCK);
      _r.fifo[t]=f[1];
      sprintf(fifoName,"%s%s%02X",options.chanPath,CHANNELNAME,t);
      if (!_runFifo(t,f[0],fifoName))
	{
	  return FALSE;
	}
    }
  return TRUE;
}
// ====================================================================================================
static void _removeFifoTasks(void)

/* Destroy the per-port sub-processes */

{
  int statloc;
  int remainingProcesses=0;
  char fifoName[PATH_MAX];

  for (int t=0; t<options.nChannels; t++)
    {
      if (_r.fifo[t]>0)
	{
	  close(_r.fifo[t]);
	  sprintf(fifoName,"%s%s%02X",options.chanPath,CHANNELNAME,t);
	  unlink(fifoName);
	  remainingProcesses++;
	}
    }

  while (remainingProcesses--)
    {
      waitpid(-1,&statloc,0);
    }
}
// ====================================================================================================
// ====================================================================================================
// ====================================================================================================
// Handlers for each message type
// ====================================================================================================
// ====================================================================================================
// ====================================================================================================
void _handleSWIT(uint8_t addr, uint8_t length, uint8_t *d)

{
  if (addr<options.nChannels)
    write(_r.fifo[addr],d,length);

  //  if (addr==0)
  //  fprintf(stdout,"%c",*d);
}
// ====================================================================================================
void _handleTS(uint8_t length, uint8_t *d)

{

}
// ====================================================================================================
// ====================================================================================================
// ====================================================================================================
// Protocol pump for decoding messages
// ====================================================================================================
// ====================================================================================================
// ====================================================================================================
enum _protoState {ITM_IDLE, ITM_SYNCING, ITM_TS, ITM_SWIT};

#ifdef PRINT_TRANSITIONS
static char *_protoNames[]={"IDLE", "SYNCING","TS","SWIT"};
#endif

void _protocolPump(uint8_t *c)

{
  static enum _protoState p;
  static int targetCount, currentCount, srcAddr;
  static uint8_t rxPacket[5];

#ifdef PRINT_TRANSITIONS
  printf("%02x %s --> ",*c,_protoNames[p]);
#endif

  switch (p)
    {
      // -----------------------------------------------------
    case ITM_IDLE:
      if (*c==0b01110000)
	{
	  /* This is an overflow packet */
	  if (options.verbose)
	    fprintf(stderr,"Overflow!\n");
	  break;
	}
      // **********
      if (*c==0)
	{
	  /* This is a sync packet - expect to see 4 more 0's followed by 0x80 */
	  targetCount=4;
	  currentCount=0;
	  p=ITM_SYNCING;
	  break;
	}
      // **********
      if (!(*c&0x0F))
	{
	  currentCount=1;
	  /* This is a timestamp packet */
	  rxPacket[0]=*c;

	  if (!(*c&0x80))
	    {
	      /* A one byte output */
	      _handleTS(currentCount,rxPacket);
	    }
	  else
	    {
	      p=ITM_TS;
	    }
	  break;
	}
      // **********
      if ((*c&0x0F) == 0x04)
	{
	  /* This is a reserved packet */
	  break;
	}
      // **********
      if (!(*c&0x04))
	{
	  /* This is a SWIT packet */
	  if ((targetCount=*c&0x03)==3)
	    targetCount=4;
	  srcAddr=(*c&0xF8)>>3;
	  currentCount=0;
	  p=ITM_SWIT;
	  break;
	}
      // **********
      if (options.verbose)
	fprintf(stderr,"Illegal packet start in IDLE state\n");
      break;
      // -----------------------------------------------------
    case ITM_SWIT:
	  rxPacket[currentCount]=*c;
	  currentCount++;

	  if (currentCount>=targetCount)
	    {
	      p=ITM_IDLE;
	      _handleSWIT(srcAddr, targetCount, rxPacket);
	    }
	  break;
      // -----------------------------------------------------
    case ITM_TS:
      rxPacket[currentCount++]=*c;
      if (!(*c&0x80))
	{
	  /* We are done */
	  _handleTS(currentCount,rxPacket);
	}
      else
	{
	  if (currentCount>4)
	    {
	      /* Something went badly wrong */
	      p=ITM_IDLE;
	    }
	  break;
	}

      // -----------------------------------------------------
    case ITM_SYNCING:
      if ((*c==0) && (currentCount<targetCount))
	{
	  currentCount++;
	}
      else
	{
	  if (*c==0x80)
	    {
	      p=ITM_IDLE;
	    }
	  else
	    {
	      /* This should really be an UNKNOWN state */
	      p=ITM_IDLE;
	    }
	}
      break;
      // -----------------------------------------------------
    }
#ifdef PRINT_TRANSITIONS
  printf("%s\n",_protoNames[p]);
#endif
}
// ====================================================================================================
void intHandler(int dummy)

{
  exit(0);
}
// ====================================================================================================
void _printHelp(char *progName)

{
  printf("Useage: %s <dhnv> <b basedir> <p port> <s speed>\n",progName);
  printf("        b: <basedir> for channels\n");
  printf("        h: This help\n");
  printf("        d: Dump received data without further processing\n");
  printf("        n: <Number> of channels to populate\n");
  printf("        p: <serialPort> to use\n");
  printf("        s: <serialSpeed> to use\n");
  printf("        v: Verbose mode\n");
}
// ====================================================================================================
int _processOptions(int argc, char *argv[])

{
  int c;
  while ((c = getopt (argc, argv, "vdn:b:hp:s:")) != -1)
    switch (c)
      {
      case 'v':
        options.verbose = 1;
        break;
      case 'd':
        options.dump = 1;
        break;
      case 'p':
	options.port=optarg;
	break;
      case 's':
	options.speed=atoi(optarg);
	break;
      case 'h':
	_printHelp(argv[0]);
	return FALSE;
      case 'n':
	options.nChannels=atoi(optarg);
	if ((options.nChannels<1) || (options.nChannels>MAX_FIFOS))
	  {
	    fprintf(stderr,"Number of channels out of range (1..%d)\n",MAX_FIFOS);
	    return FALSE;
	  }
	break;
      case 'b':
        options.chanPath = optarg;
        break;
      case '?':
        if (optopt == 'b')
          fprintf (stderr, "Option '%c' requires an argument.\n", optopt);
        else if (!isprint (optopt))
	    fprintf (stderr,"Unknown option character `\\x%x'.\n", optopt);
	return FALSE;
      default:
        return FALSE;
      }

  if (options.verbose)
    {
      fprintf(stdout,"Verbose: TRUE\nBasePath: %s\n",options.chanPath);
      if (options.port)
	{
	  fprintf(stdout,"Serial Port: %s\nSerial Speed: %d\n",options.port,options.speed);
	}
    }
  return TRUE;
}
// ====================================================================================================
int usbFeeder(void)

{

  unsigned char cbw[TRANSFER_SIZE];
  libusb_device_handle *handle;
  libusb_device *dev;
  int size;

  while (1)
    {
      if (libusb_init(NULL) < 0)
	{
	  fprintf(stderr,"Failed to initalise USB interface\n");
	  return (-1);
	}

      while (!(handle = libusb_open_device_with_vid_pid(NULL, VID, PID)))
	{
	  usleep(500000);
	}

      if (!(dev = libusb_get_device(handle)))
	continue;

      if (libusb_claim_interface (handle, INTERFACE)<0)
	continue;

      while (0==libusb_bulk_transfer(handle, ENDPOINT, cbw, TRANSFER_SIZE, &size, 10))
	{
	  unsigned char *c=cbw;
          if (options.dump)
          {
              cbw[size] = 0;
              printf("%s", (char*)cbw);
          }
          else
              while (size--)
                  _protocolPump(c++);
	}

      libusb_close(handle);
    }
}
// ====================================================================================================
int serialFeeder(void)

{
  int f;
  unsigned char cbw[TRANSFER_SIZE];
  ssize_t t;
  struct termios settings;

  while (1)
    {
      while ((f=open(options.port,O_RDONLY))<0)
	{
	  if (options.verbose)
	    {
	      fprintf(stderr,"Can't open serial port\n");
	    }
	  usleep(500000);
	}

      if (options.verbose)
	{
	  fprintf(stderr,"Port opened\n");
	}

      if (tcgetattr(f, &settings) <0)
	{
	  perror("tcgetattr");
	  return(-3);
	}

      if (cfsetspeed(&settings, options.speed)<0)
	{
	  perror("Setting input speed");
	  return -3;
	}
      settings.c_lflag &= ~(ICANON | ECHO | ECHOE | ISIG);
      settings.c_cflag &= ~PARENB; /* no parity */
      settings.c_cflag &= ~CSTOPB; /* 1 stop bit */
      settings.c_cflag &= ~CSIZE;
      settings.c_cflag |= CS8 | CLOCAL; /* 8 bits */
      settings.c_oflag &= ~OPOST; /* raw output */

      if (tcsetattr(f, TCSANOW, &settings)<0)
	{
	  fprintf(stderr,"Unsupported baudrate\n");
	  exit(-3);
	}

      tcflush(f, TCOFLUSH);

      while ((t=read(f,cbw,TRANSFER_SIZE))>0)
	{
	  unsigned char *c=cbw;
	  while (t--)
	    _protocolPump(c++);
	}
      if (options.verbose)
	{
	  fprintf(stderr,"Read failed\n");
	}
      close(f);
    }
}
// ====================================================================================================
int main(int argc, char *argv[])

{
  if (!_processOptions(argc,argv))
    {
      exit(-1);
    }

  atexit(_removeFifoTasks);
  /* This ensures the atexit gets called */
  signal(SIGINT, intHandler);
  if (!_makeFifoTasks())
    {
      fprintf(stderr,"Failed to make channel devices\n");
      exit(-1);
    }

  /* Using the exit construct rather than return ensures the atexit gets called */
  if (!options.port)
    exit(usbFeeder());
  else
    exit(serialFeeder());
  fprintf(stderr,"Returned\n");
  exit(0);
}
// ====================================================================================================
