TUDSSL/DIPS/int-debugger-firmware/include/target.h

/*
* This file is part of the Black Magic Debug project.
*
* Copyright (C) 2016  Black Sphere Technologies Ltd.
* Written by Gareth McMullin <gareth@blacksphere.co.nz>
*
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
* You should have received a copy of the GNU General Public License
* along with this program.  If not, see <http://www.gnu.org/licenses/>.
*/

/* Provides an abstract 'target object', the 'methods' of which must be
* implemented by a target driver when a supported device is detected.
*/

#ifndef INCLUDE_TARGET_H
#define INCLUDE_TARGET_H

#include <stdarg.h>
#include <stdbool.h>
#include <stdint.h>
#include <sys/types.h>
#include "intermittent.h"

typedef struct target_s target;
typedef uint32_t target_addr_t;
struct target_controller;

uint32_t adiv5_swdp_scan(uint32_t targetid);
uint32_t jtag_scan(const uint8_t *lrlens);
uint32_t sbw_scan(uint32_t targetid);

int target_foreach(void (*cb)(int i, target *t, void *context), void *context);
void target_list_free(void);
void target_list_free_extended(void);
bool target_available(void);
void target_lost(void);

/* Attach/detach functions */
target *target_attach(target *t, struct target_controller *);
target *target_attach_n(size_t n, struct target_controller *);
void target_detach(target *t);
bool target_attached(target *t);
const char *target_driver_name(target *t);
const char *target_core_name(target *t);
unsigned int target_designer(target *t);
unsigned int target_part_id(target *t);

/* Memory access functions */
bool target_mem_map(target *t, char *buf, size_t len);
int target_mem_read(target *t, void *dest, target_addr_t src, size_t len);
int target_mem_write(target *t, target_addr_t dest, const void *src, size_t len);
/* Flash memory access functions */
bool target_flash_erase(target *t, target_addr_t addr, size_t len);
bool target_flash_write(target *t, target_addr_t dest, const void *src, size_t len);
bool target_flash_complete(target *t);

/* Register access functions */
size_t target_regs_size(target *t);
const char *target_tdesc(target *t);
void target_regs_read(target *t, void *data);
void target_regs_write(target *t, const void *data);
ssize_t target_reg_read(target *t, int reg, void *data, size_t max);
ssize_t target_reg_write(target *t, int reg, const void *data, size_t size);

/* Halt/resume functions */
enum target_halt_reason {
   TARGET_HALT_RUNNING = 0, /* Target not halted */
   TARGET_HALT_ERROR,       /* Failed to read target status */
   TARGET_HALT_REQUEST,
   TARGET_HALT_STEPPING,
   TARGET_HALT_BREAKPOINT,
   TARGET_HALT_WATCHPOINT,
   TARGET_HALT_FAULT,
   TARGET_HALT_INTERMITTENT,
};

void target_reset(target *t);
void target_halt_request(target *t);
enum target_halt_reason target_halt_poll(target *t, target_addr_t *watch);
void target_halt_resume(target *t, bool step);
void target_set_cmdline(target *t, char *cmdline);
void target_set_heapinfo(
                      target *t, target_addr_t heap_base, target_addr_t heap_limit, target_addr_t stack_base, target_addr_t stack_limit);

/* Break-/watchpoint functions */
enum target_breakwatch {
   TARGET_BREAK_SOFT,
   TARGET_BREAK_HARD,
   TARGET_WATCH_WRITE,
   TARGET_WATCH_READ,
   TARGET_WATCH_ACCESS,
};
int target_breakwatch_set(target *t, enum target_breakwatch, target_addr_t, size_t, bool update_heap);
int target_breakwatch_clear(target *t, enum target_breakwatch, target_addr_t, size_t);
int target_restore_breakpoints(target *t);

/* Command interpreter */
void target_command_help(target *t);
int target_command(target *t, int argc, const char *argv[]);

/* keep target_errno in sync with errno values in gdb/include/gdb/fileio.h */
enum target_errno {
   TARGET_EPERM = 1,
   TARGET_ENOENT = 2,
   TARGET_EINTR = 4,
   TARGET_EIO = 5,
   TARGET_EBADF = 9,
   TARGET_EACCES = 13,
   TARGET_EFAULT = 14,
   TARGET_EBUSY = 16,
   TARGET_EEXIST = 17,
   TARGET_ENODEV = 19,
   TARGET_ENOTDIR = 20,
   TARGET_EISDIR = 21,
   TARGET_EINVAL = 22,
   TARGET_ENFILE = 23,
   TARGET_EMFILE = 24,
   TARGET_EFBIG = 27,
   TARGET_ENOSPC = 28,
   TARGET_ESPIPE = 29,
   TARGET_EROFS = 30,
   TARGET_ENOSYS = 88,
   TARGET_ENAMETOOLONG = 91,
   TARGET_EUNKNOWN = 9999,
};

enum target_open_flags {
   TARGET_O_RDONLY = 0,
   TARGET_O_WRONLY = 1,
   TARGET_O_RDWR = 2,
   TARGET_O_APPEND = 0x008,
   TARGET_O_CREAT = 0x200,
   TARGET_O_TRUNC = 0x400,
};

enum target_seek_flag {
   TARGET_SEEK_SET = 0,
   TARGET_SEEK_CUR = 1,
   TARGET_SEEK_END = 2,
};

struct target_controller {
   void (*destroy_callback)(struct target_controller *, target *t);
   void (*printf)(struct target_controller *, const char *fmt, va_list);

   /* Interface to host system calls */
   int (*open)(
       struct target_controller *, target_addr_t path, size_t path_len, enum target_open_flags flags, mode_t mode);
   int (*close)(struct target_controller *, int fd);
   int (*read)(struct target_controller *, int fd, target_addr_t buf, unsigned int count);
   int (*write)(struct target_controller *, int fd, target_addr_t buf, unsigned int count);
   long (*lseek)(struct target_controller *, int fd, long offset, enum target_seek_flag flag);
   int (*rename)(
       struct target_controller *, target_addr_t oldpath, size_t old_len, target_addr_t newpath, size_t new_len);
   int (*unlink)(struct target_controller *, target_addr_t path, size_t path_len);
   int (*stat)(struct target_controller *, target_addr_t path, size_t path_len, target_addr_t buf);
   int (*fstat)(struct target_controller *, int fd, target_addr_t buf);
   int (*gettimeofday)(struct target_controller *, target_addr_t tv, target_addr_t tz);
   int (*isatty)(struct target_controller *, int fd);
   int (*system)(struct target_controller *, target_addr_t cmd, size_t cmd_len);
   enum target_errno errno_;
   bool interrupted;
};

#endif /* INCLUDE_TARGET_H */
