TUDSSL/DIPS/int-debugger-firmware/src/crc32.c

/*
* This file is part of the Black Magic Debug project.
*
* Copyright (C) 2011  Black Sphere Technologies Ltd.
* Written by Gareth McMullin <gareth@blacksphere.co.nz>
*
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
* You should have received a copy of the GNU General Public License
* along with this program.  If not, see <http://www.gnu.org/licenses/>.
*/

#include "general.h"
#include "target.h"
#include "gdb_if.h"

#if !defined(STM32F0) && !defined(STM32F1) && !defined(STM32F2) && \
   !defined(STM32F3) && !defined(STM32F4) && !defined(STM32F7) && \
   !defined(STM32L0) && !defined(STM32L1) && !defined(STM32F4) && \
   !defined(STM32G0) && !defined(STM32G4)
static const uint32_t crc32_table[] = {
   0x00000000, 0x04C11DB7, 0x09823B6E, 0x0D4326D9,
   0x130476DC, 0x17C56B6B, 0x1A864DB2, 0x1E475005,
   0x2608EDB8, 0x22C9F00F, 0x2F8AD6D6, 0x2B4BCB61,
   0x350C9B64, 0x31CD86D3, 0x3C8EA00A, 0x384FBDBD,
   0x4C11DB70, 0x48D0C6C7, 0x4593E01E, 0x4152FDA9,
   0x5F15ADAC, 0x5BD4B01B, 0x569796C2, 0x52568B75,
   0x6A1936C8, 0x6ED82B7F, 0x639B0DA6, 0x675A1011,
   0x791D4014, 0x7DDC5DA3, 0x709F7B7A, 0x745E66CD,
   0x9823B6E0, 0x9CE2AB57, 0x91A18D8E, 0x95609039,
   0x8B27C03C, 0x8FE6DD8B, 0x82A5FB52, 0x8664E6E5,
   0xBE2B5B58, 0xBAEA46EF, 0xB7A96036, 0xB3687D81,
   0xAD2F2D84, 0xA9EE3033, 0xA4AD16EA, 0xA06C0B5D,
   0xD4326D90, 0xD0F37027, 0xDDB056FE, 0xD9714B49,
   0xC7361B4C, 0xC3F706FB, 0xCEB42022, 0xCA753D95,
   0xF23A8028, 0xF6FB9D9F, 0xFBB8BB46, 0xFF79A6F1,
   0xE13EF6F4, 0xE5FFEB43, 0xE8BCCD9A, 0xEC7DD02D,
   0x34867077, 0x30476DC0, 0x3D044B19, 0x39C556AE,
   0x278206AB, 0x23431B1C, 0x2E003DC5, 0x2AC12072,
   0x128E9DCF, 0x164F8078, 0x1B0CA6A1, 0x1FCDBB16,
   0x018AEB13, 0x054BF6A4, 0x0808D07D, 0x0CC9CDCA,
   0x7897AB07, 0x7C56B6B0, 0x71159069, 0x75D48DDE,
   0x6B93DDDB, 0x6F52C06C, 0x6211E6B5, 0x66D0FB02,
   0x5E9F46BF, 0x5A5E5B08, 0x571D7DD1, 0x53DC6066,
   0x4D9B3063, 0x495A2DD4, 0x44190B0D, 0x40D816BA,
   0xACA5C697, 0xA864DB20, 0xA527FDF9, 0xA1E6E04E,
   0xBFA1B04B, 0xBB60ADFC, 0xB6238B25, 0xB2E29692,
   0x8AAD2B2F, 0x8E6C3698, 0x832F1041, 0x87EE0DF6,
   0x99A95DF3, 0x9D684044, 0x902B669D, 0x94EA7B2A,
   0xE0B41DE7, 0xE4750050, 0xE9362689, 0xEDF73B3E,
   0xF3B06B3B, 0xF771768C, 0xFA325055, 0xFEF34DE2,
   0xC6BCF05F, 0xC27DEDE8, 0xCF3ECB31, 0xCBFFD686,
   0xD5B88683, 0xD1799B34, 0xDC3ABDED, 0xD8FBA05A,
   0x690CE0EE, 0x6DCDFD59, 0x608EDB80, 0x644FC637,
   0x7A089632, 0x7EC98B85, 0x738AAD5C, 0x774BB0EB,
   0x4F040D56, 0x4BC510E1, 0x46863638, 0x42472B8F,
   0x5C007B8A, 0x58C1663D, 0x558240E4, 0x51435D53,
   0x251D3B9E, 0x21DC2629, 0x2C9F00F0, 0x285E1D47,
   0x36194D42, 0x32D850F5, 0x3F9B762C, 0x3B5A6B9B,
   0x0315D626, 0x07D4CB91, 0x0A97ED48, 0x0E56F0FF,
   0x1011A0FA, 0x14D0BD4D, 0x19939B94, 0x1D528623,
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
};

static uint32_t crc32_calc(uint32_t crc, uint8_t data)
{
   return (crc << 8) ^ crc32_table[((crc >> 24) ^ data) & 255];
}

int generic_crc32(target *t, uint32_t *crc_res, uint32_t base, size_t len)
{
   uint32_t crc = -1;
#if PC_HOSTED == 1
   /* Reading a 2 MByte on a H743 takes about 80 s@128, 28s @ 1k,
    * 22 s @ 4k and 21 s @ 64k
    */
   uint8_t bytes[0x1000];
#else
   uint8_t bytes[128];
#endif
#if defined(ENABLE_DEBUG)
   uint32_t start_time = platform_time_ms();
#endif
   uint32_t last_time = platform_time_ms();
   while (len) {
       uint32_t actual_time = platform_time_ms();
       if ( actual_time > last_time + 1000) {
           last_time = actual_time;
           gdb_if_putchar(0, true);
       }
       size_t read_len = MIN(sizeof(bytes), len);
       if (target_mem_read(t, bytes, base, read_len)) {
           DEBUG_WARN("generic_crc32 error around address 0x%08" PRIx32 "\n",
                      base);
           return -1;
       }

       for (unsigned i = 0; i < read_len; i++)
           crc = crc32_calc(crc, bytes[i]);

       base += read_len;
       len -= read_len;
   }
   DEBUG_WARN("%" PRIu32 " ms\n", platform_time_ms() - start_time);
   *crc_res = crc;
   return 0;
}
#else
#include <libopencm3/stm32/crc.h>
int generic_crc32(target *t, uint32_t *crc_res, uint32_t base, size_t len)
{
   uint8_t bytes[128];
   uint32_t crc;

   CRC_CR |= CRC_CR_RESET;

   uint32_t last_time = platform_time_ms();
   while (len > 3) {
       uint32_t actual_time = platform_time_ms();
       if ( actual_time > last_time + 1000) {
           last_time = actual_time;
           gdb_if_putchar(0, true);
       }
       size_t read_len = MIN(sizeof(bytes), len) & ~3;
       if (target_mem_read(t, bytes, base, read_len)) {
           DEBUG_WARN("generic_crc32 error around address 0x%08" PRIx32 "\n",
                      base);
           return -1;
       }

       for (unsigned i = 0; i < read_len; i += 4)
           CRC_DR = __builtin_bswap32(*(uint32_t*)(bytes+i));

       base += read_len;
       len -= read_len;
   }

   crc = CRC_DR;

   if (target_mem_read(t, bytes, base, len)) {
       DEBUG_WARN("generic_crc32 error around address 0x%08" PRIx32 "\n",
                  base);
       return -1;
   }
   uint8_t *data = bytes;
   while (len--) {
       crc ^= *data++ << 24;
       for (int i = 0; i < 8; i++) {
           if (crc & 0x80000000)
               crc = (crc << 1) ^ 0x4C11DB7;
           else
               crc <<= 1;
       }
   }
   *crc_res = crc;
   return 0;
}
#endif
