TUDSSL/DIPS/int-debugger-firmware/src/platforms/stm32/gdb_if.c

/*
 * This file is part of the Black Magic Debug project.
 *
 * Copyright (C) 2011  Black Sphere Technologies Ltd.
 * Written by Gareth McMullin <gareth@blacksphere.co.nz>
 *
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
 * You should have received a copy of the GNU General Public License
 * along with this program.  If not, see <http://www.gnu.org/licenses/>.
 */

/* This file implements a transparent channel over which the GDB Remote
 * Serial Debugging protocol is implemented.  This implementation for STM32
 * uses the USB CDC-ACM device bulk endpoints to implement the channel.
 */

#include <libopencmsis/core_cm3.h>

#include "general.h"
#include "platforms/common/usb_serial.h"
#include "gdb_if.h"

static uint32_t count_out;
static uint32_t count_in;
static uint32_t out_ptr;
static uint8_t buffer_out[CDCACM_PACKET_SIZE];
static uint8_t buffer_in[CDCACM_PACKET_SIZE];

void gdb_if_putchar(unsigned char c, int flush)
{
	buffer_in[count_in++] = c;
	if (flush || (count_in == CDCACM_PACKET_SIZE)) {
		/* Refuse to send if USB isn't configured, and
		 * don't bother if nobody's listening */
		if (usb_get_config() != 1 || !gdb_serial_get_dtr()) {
			count_in = 0;
			return;
		}
		while (usbd_ep_write_packet(usbdev, CDCACM_GDB_ENDPOINT, buffer_in, count_in) <= 0)
			continue;

		if (flush && (count_in == CDCACM_PACKET_SIZE)) {
			/* We need to send an empty packet for some hosts
			 * to accept this as a complete transfer. */
			/* libopencm3 needs a change for us to confirm when
			 * that transfer is complete, so we just send a packet
			 * containing a null byte for now.
			 */
			while (usbd_ep_write_packet(usbdev, CDCACM_GDB_ENDPOINT, "\0", 1) <= 0)
				continue;
		}

		count_in = 0;
	}
}

static void gdb_if_update_buf(void)
{
	while (usb_get_config() != 1);
	count_out = usbd_ep_read_packet(usbdev, CDCACM_GDB_ENDPOINT,
	                                buffer_out, CDCACM_PACKET_SIZE);
	out_ptr = 0;
	if (!count_out)
		__WFI();}

unsigned char gdb_if_getchar(void)
{

	while (!(out_ptr < count_out)) {
		/* Detach if port closed */
		if (!gdb_serial_get_dtr()) {
			__WFI();
			return 0x04;
		}

		gdb_if_update_buf();
	}

	return buffer_out[out_ptr++];
}

unsigned char gdb_if_getchar_to(int timeout)
{
	platform_timeout t;
	platform_timeout_set(&t, timeout);

	if (!(out_ptr < count_out)) do {
		/* Detach if port closed */
			if (!gdb_serial_get_dtr()) {
				__WFI(); /* systick will wake up too!*/
				return 0x04;
			}

		gdb_if_update_buf();
	} while (!platform_timeout_is_expired(&t) && !(out_ptr < count_out));

	if(out_ptr < count_out)
		return gdb_if_getchar();

	return -1;
}
