TUDSSL/DIPS/int-debugger-emulator/platforms/int-debug-v1-0.c

#include "platform.h"

static void GPIO_Init(void);
static void SystemClock_Config(void);

/**
 * Configure system clocks and GPIO
 */
void systemConfig(void) {
  /* Configure the system clock */
  SystemClock_Config();

  GPIO_Init();

    /* DMA controller clock enable */
    __HAL_RCC_DMA2_CLK_ENABLE();
    __HAL_RCC_DMA1_CLK_ENABLE();
}

/**
 * @brief System Clock Configuration
 * @retval None
 */
static void SystemClock_Config(void) {
    RCC_OscInitTypeDef RCC_OscInitStruct = {0};
    RCC_ClkInitTypeDef RCC_ClkInitStruct = {0};
    RCC_PeriphCLKInitTypeDef PeriphClkInit = {0};

  /** Initializes the RCC Oscillators according to the specified parameters
   * in the RCC_OscInitTypeDef structure.
   */
  RCC_OscInitStruct.OscillatorType = RCC_OSCILLATORTYPE_HSE;
  RCC_OscInitStruct.HSEState = RCC_HSE_ON;
  RCC_OscInitStruct.HSEPredivValue = RCC_HSE_PREDIV_DIV1;
  RCC_OscInitStruct.HSIState = RCC_HSI_ON;
  RCC_OscInitStruct.PLL.PLLState = RCC_PLL_ON;
  RCC_OscInitStruct.PLL.PLLSource = RCC_PLLSOURCE_HSE;
  RCC_OscInitStruct.PLL.PLLMUL = RCC_PLL_MUL9;
  if (HAL_RCC_OscConfig(&RCC_OscInitStruct) != HAL_OK) {
    Error_Handler();
  }
  /** Initializes the CPU, AHB and APB buses clocks
   */
  RCC_ClkInitStruct.ClockType = RCC_CLOCKTYPE_HCLK | RCC_CLOCKTYPE_SYSCLK |
                                RCC_CLOCKTYPE_PCLK1 | RCC_CLOCKTYPE_PCLK2;
  RCC_ClkInitStruct.SYSCLKSource = RCC_SYSCLKSOURCE_PLLCLK;
  RCC_ClkInitStruct.AHBCLKDivider = RCC_SYSCLK_DIV1;
  RCC_ClkInitStruct.APB1CLKDivider = RCC_HCLK_DIV2;
  RCC_ClkInitStruct.APB2CLKDivider = RCC_HCLK_DIV1;

  if (HAL_RCC_ClockConfig(&RCC_ClkInitStruct, FLASH_LATENCY_2) != HAL_OK) {
    Error_Handler();
  }
  PeriphClkInit.PeriphClockSelection = RCC_PERIPHCLK_USB | RCC_PERIPHCLK_SDADC;
  PeriphClkInit.USBClockSelection = RCC_USBCLKSOURCE_PLL_DIV1_5;
  PeriphClkInit.SdadcClockSelection = RCC_SDADCSYSCLK_DIV12;
  if (HAL_RCCEx_PeriphCLKConfig(&PeriphClkInit) != HAL_OK) {
    Error_Handler();
  }
  HAL_PWREx_EnableSDADC(PWR_SDADC_ANALOG1);
  HAL_PWREx_EnableSDADC(PWR_SDADC_ANALOG2);
  HAL_PWREx_EnableSDADC(PWR_SDADC_ANALOG3);
}

/**
 * @brief GPIO Initialization Function
 * @param None
 * @retval None
 */
static void GPIO_Init(void) {
  GPIO_InitTypeDef GPIO_InitStruct = {0};

  /* GPIO Ports Clock Enable */
  __HAL_RCC_GPIOF_CLK_ENABLE();
  __HAL_RCC_GPIOA_CLK_ENABLE();
  __HAL_RCC_GPIOB_CLK_ENABLE();
  __HAL_RCC_GPIOE_CLK_ENABLE();

  /*Configure GPIO pin : PIN_INT_Pin */
  // This pin is alternating, both systems can pull them up for activating a breakpoint
  GPIO_InitStruct.Pin = PIN_INT_Pin;
  GPIO_InitStruct.Mode = GPIO_MODE_IT_RISING_FALLING;
  GPIO_InitStruct.Pull = GPIO_NOPULL;
  HAL_GPIO_Init(PIN_INT_GPIO_Port, &GPIO_InitStruct);

  /* EXTI interrupt init*/
  HAL_NVIC_SetPriority(EXTI9_5_IRQn, 0, 0);
  HAL_NVIC_EnableIRQ(EXTI9_5_IRQn);
}
