TUDSSL/DIPS/measurements/userstudy/int-debugger-user-study-debugcode/wisp_version/src/checkpointing.h

#ifndef USERTESTING_WISP_BASE_CHECKPOINTING_H
#define USERTESTING_WISP_BASE_CHECKPOINTING_H
#include "stdint.h"

int restore();

void checkpoint(uint16_t taskID);

#endif //USERTESTING_WISP_BASE_CHECKPOINTING_H
