TUDSSL/DIPS/measurements/userstudy/int-debugger-user-study-debugcode/wisp_version/src/tasks/naturalSum.h

//
// Created by tomh on 11-6-22.
//

#ifndef USERTESTING_WISP_BASE_NATURALSUM_H
#define USERTESTING_WISP_BASE_NATURALSUM_H

void execute_gauss_sum();
void execute_natural_sum();
int gauss_result();

#endif //USERTESTING_WISP_BASE_NATURALSUM_H
